CR-Formula/FSAEElectrical/Module Tests/Lora/Receiver/Receiver.ino

#include <SPI.h>
#include <RH_RF95.h>

// Uno
#define RFM95_CS    4
#define RFM95_INT   3
#define RFM95_RST   2

#define RF95_FREQ 915.0

typedef struct data_struct
{
  uint8_t RPM;            // RPM
  uint32_t TPS;           // TPS
  uint32_t FOT;           // Fuel Open Time
  uint32_t IA;            // Ignition Angle
  uint32_t Lam;           // Lambda
  uint32_t AirT;          // Air Temp
  uint32_t CoolT;         // Coolant Temp
  uint32_t Speed;         // Vehicle Speed
  uint32_t OilP;          // Oil Pressure
  uint32_t FuelP;         // Fuel Pressure
  uint32_t FLTemp;        // Front Left Brake Temp
  uint32_t FRTemp;        // Front Right Brake Temp
  uint32_t RLTemp;        // Rear Left Brake Temp
  uint32_t RRTemp;        // Rear Right Brake Temp
  uint32_t FRPot;         // Front Right Suspension Damper
  uint32_t FLPot;         // Front Left Suspension Damper
  uint32_t RRPot;         // Rear Right Suspension Damper
  uint32_t RLPot;         // Rear Left Suspension Damper
  uint32_t BrakeFront;    // Front Brake Pressure
  uint32_t BrakeRear;     // Rear Brake Pressure
  uint32_t AccX;          // Accelerometer X Axis
  uint32_t AccY;          // Accelerometer Y Axis
  uint32_t AccZ;          // Accelerometer Z Axis
} data_struct;
data_struct telemetry;

RH_RF95 rf95(RFM95_CS, RFM95_INT);

void setup() {
  pinMode(LED_BUILTIN, OUTPUT);
  pinMode(RFM95_RST, OUTPUT);
  digitalWrite(RFM95_RST, HIGH);

  Serial.begin(115200);
  while (!Serial) delay(1);
  delay(100);

  Serial.println("LoRa RX Test!");

  digitalWrite(RFM95_RST, LOW);
  delay(10);
  digitalWrite(RFM95_RST, HIGH);
  delay(10);

  while (!rf95.init()) {
    Serial.println("LoRa radio init failed");
    while (1);
  }
  Serial.println("LoRa radio init OK!");

  if (!rf95.setFrequency(RF95_FREQ)) {
    Serial.println("setFrequency failed");
    while (1);
  }
  Serial.print("Set Freq to: "); Serial.println(RF95_FREQ);
  rf95.setTxPower(23, false);
}

void loop() {
  if (rf95.available()) { // Check for new message
    uint8_t buf[sizeof(telemetry)]; // buffer for message
    uint8_t len = sizeof(buf);

    if (rf95.recv(buf, &len)) {
      memcpy(&telemetry, buf, sizeof(telemetry)); // Copy the message into the data struct
      // Print out the data struct
      Serial.println("Data:");
      Serial.println(telemetry.RPM);
      Serial.println(telemetry.TPS);
      Serial.println(telemetry.FOT);
      Serial.println(telemetry.IA);
      Serial.println(telemetry.Lam);
      Serial.println(telemetry.AirT);
      Serial.println(telemetry.CoolT);
      Serial.println(telemetry.Speed);
      Serial.println(telemetry.OilP);
      Serial.println(telemetry.FuelP);
      Serial.println(telemetry.FLTemp);
      Serial.println(telemetry.FRTemp);
      Serial.println(telemetry.RLTemp);
      Serial.println(telemetry.RRTemp);
      Serial.println(telemetry.FRPot);
      Serial.println(telemetry.FLPot);
      Serial.println(telemetry.RRPot);
      Serial.println(telemetry.RLPot);
      Serial.println(telemetry.BrakeFront);
      Serial.println(telemetry.BrakeRear);
      Serial.println(telemetry.AccX);
      Serial.println(telemetry.AccY);
      Serial.println(telemetry.AccZ);
      Serial.println("End of Data");
    }
  }
}
