CR-Formula/FSAEElectrical/Module Tests/Validation/Wireless/Wireless_Sender.ino

/*
  Rui Santos
  Complete project details at https://RandomNerdTutorials.com/esp-now-two-way-communication-esp32/
  
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
  The above copyright notice and this permission notice shall be included in all
  copies or substantial portions of the Software.
*/

#include <esp_now.h>
#include <WiFi.h>

// REPLACE WITH THE MAC Address of your receiver 
uint8_t broadcastAddress[] = {0xFF, 0xFF, 0xFF, 0xFF, 0xFF, 0xFF};

// Variable to store if sending data was successful
String success;

long startTime;
long endTime;
long totalTime;

//Structure example to send data
//Must match the receiver structure
typedef struct struct_message {
  float RPM;        // RPM value
  float TPS;        // TPS value
  float FOT;        // Fuel Open Time value
  float IA;         // Ignition Angle value
  float Lam;        // Lambda value
  float AirT;       // Air Temp value
  float CoolT;      // Coolent Temp value
  float Lat;        // Latitude
  float Lng;        // Longitude
  float Speed;      // GPS Speed
  float OilP;       // Oil Pressure
  float FuelP;      // Fuel Pressure
  float FLTemp;     // Front Left Brake Temp
  float FRTemp;     // Front Right Brake Temp
  float RLTemp;     // Rear Left Brake Temp
  float RRTemp;     // Rear Right Brake Temp
  float FRPot;      // Front Right suspension damper
  float FLPot;      // Front Left suspension damper
  float RRPot;      // Rear Right suspension damper
  float RLPot;      // Rear Left suspension damper
  float BrakeFront; // Front Brake Pressure
  float BrakeRear;  // Rear Brake Pressure
  float AccX;       // Acclerometer X Axis
  float AccY;       // Acclerometer Y Axis
  float AccZ;       // Acclerometer Z Axis
  float GyrX;       // Gyroscope X Axis
  float GyrY;       // Gyroscope Y Axis
  float GyrZ;       // Gyroscope Z Axis
} struct_message;

// Create a struct_message to hold incoming sensor readings
struct_message incomingValues;

esp_now_peer_info_t peerInfo;

// Callback when data is sent
void OnDataSent(const uint8_t *mac_addr, esp_now_send_status_t status) {
  Serial.print("\r\nLast Packet Send Status:\t");
  Serial.println(status == ESP_NOW_SEND_SUCCESS ? "Delivery Success" : "Delivery Fail");
  if (status ==0){
    success = "Delivery Success :)";
  }
  else{
    success = "Delivery Fail :(";
  }
  startTime = millis();
}

// Callback when data is received
void OnDataRecv(const uint8_t * mac, const uint8_t *incomingData, int len) {
  memcpy(&incomingReadings, incomingData, sizeof(incomingReadings));

  Serial.print("Bytes received: ");
  Serial.println(len);

  endTime = millis();
  totalTime = endTime - startTime;
  Serial.println("----------");
  Serail.println(totalTime);
}
 
void setup() {
  // Init Serial Monitor
  Serial.begin(115200);
 
  // Set device as a Wi-Fi Station
  WiFi.mode(WIFI_STA);

  // Init ESP-NOW
  if (esp_now_init() != ESP_OK) {
    Serial.println("Error initializing ESP-NOW");
    return;
  }

  // Once ESPNow is successfully Init, we will register for Send CB to
  // get the status of Trasnmitted packet
  esp_now_register_send_cb(OnDataSent);
  
  // Register peer
  memcpy(peerInfo.peer_addr, broadcastAddress, 6);
  peerInfo.channel = 0;  
  peerInfo.encrypt = false;
  
  // Add peer        
  if (esp_now_add_peer(&peerInfo) != ESP_OK){
    Serial.println("Failed to add peer");
    return;
  }
  // Register for a callback function that will be called when data is received
  esp_now_register_recv_cb(OnDataRecv);
}
 
void loop() {

  // Send message via ESP-NOW
  esp_err_t result = esp_now_send(broadcastAddress, (uint8_t *) &BME280Readings, sizeof(BME280Readings));
   
  if (result == ESP_OK) {
    Serial.println("Sent with success");
  }
  else {
    Serial.println("Error sending the data");
  }
}

void end() {
  while(1);
}
